Makeroni/Eye-of-Horus/version_2/hardware/3D_Model/Covers/Camera_Frontal-Bracket-Cover_1/Texture/Texture-Camera_Frontal-Bracket-Cover_1-v0_00.jpg

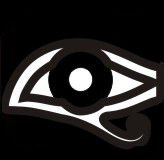
version_2/hardware/3D_Model/Covers/Camera_Frontal-Bracket-Cover_1/Texture/Texture-Camera_Frontal-Bracket-Cover_1-v0_00.jpg
