Makeroni/Eye-of-Horus/version_2/hardware/3D_Model/Covers/EoH_BackPack-Cover_1/Textures/EoH_BackPack-Cover_1-v0_00.jpg

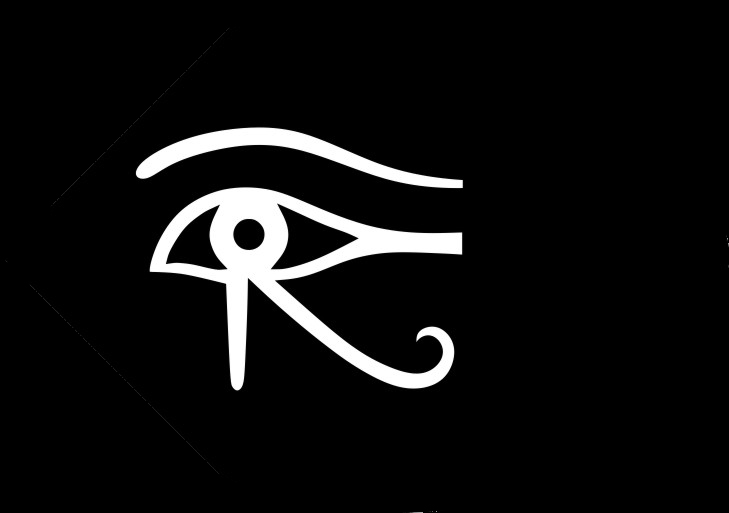
version_2/hardware/3D_Model/Covers/EoH_BackPack-Cover_1/Textures/EoH_BackPack-Cover_1-v0_00.jpg
