Makeroni/Eye-of-Horus/version_2/hardware/3D_Model/Materia_Prima/BREAKOUT_LIPO_CHARGER/Textures/Texture_Top.jpg

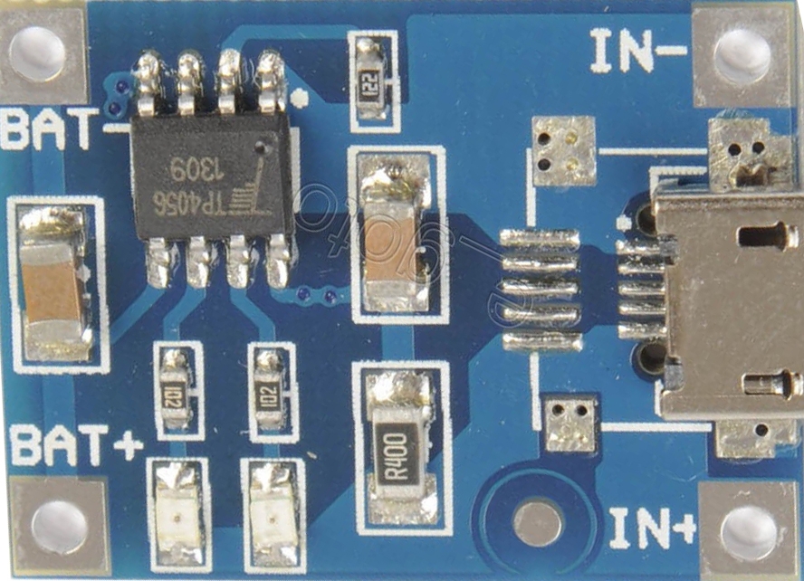
version_2/hardware/3D_Model/Materia_Prima/BREAKOUT_LIPO_CHARGER/Textures/Texture_Top.jpg
