Makeroni/Eye-of-Horus/version_2/hardware/3D_Model/Materia_Prima/DC_DC-Converter/Texture/DC_DC-Converter-Texture_Top.jpg

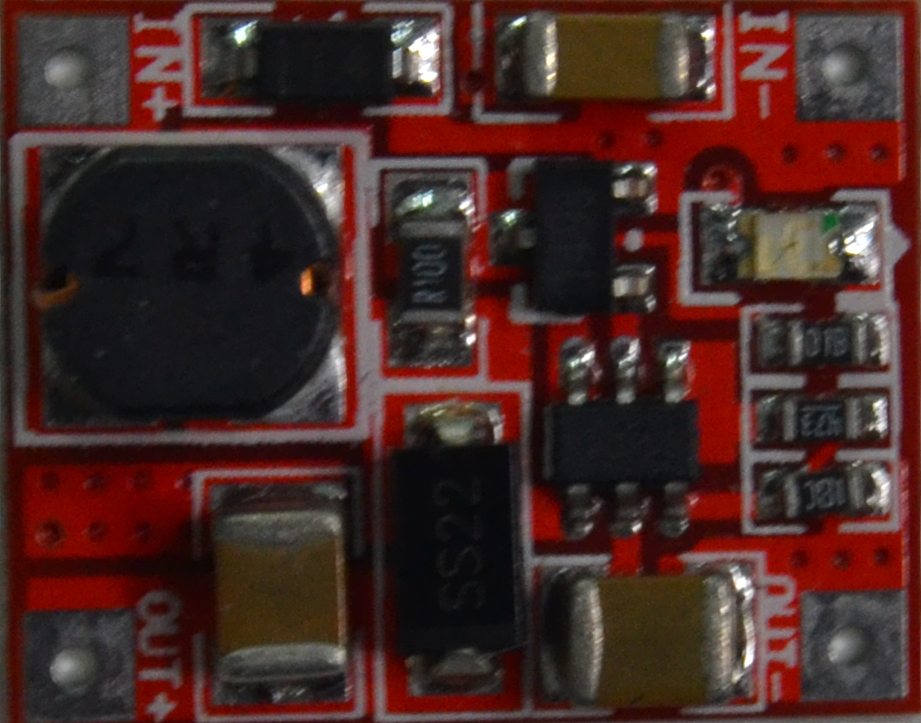
version_2/hardware/3D_Model/Materia_Prima/DC_DC-Converter/Texture/DC_DC-Converter-Texture_Top.jpg
