Makeroni/Eye-of-Horus/version_2/hardware/3D_Model/Materia_Prima/HUB_USB-2.0/Texture/HUB_USB-2_0-Texture_Bot.jpg

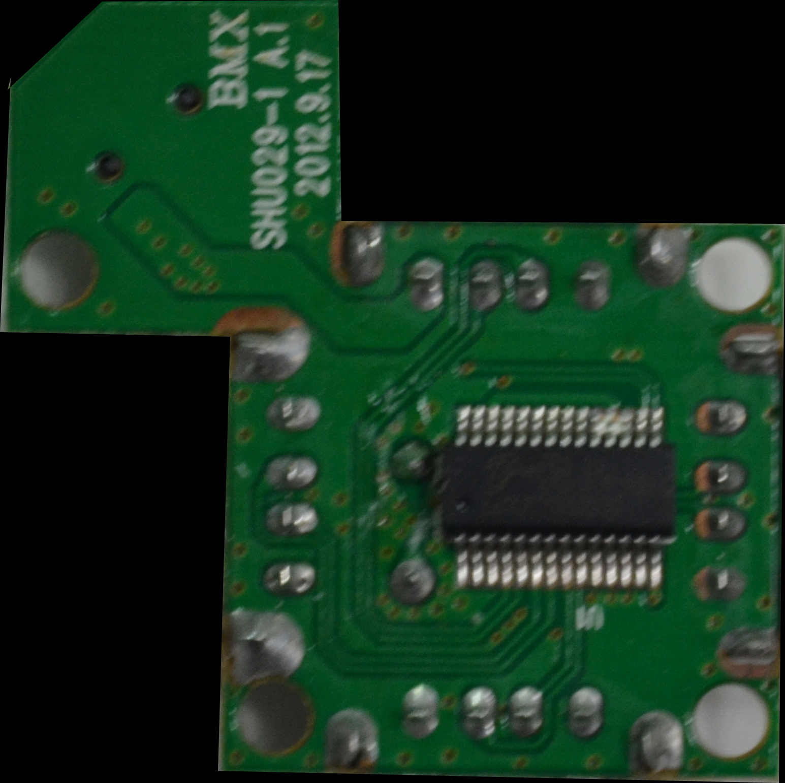
version_2/hardware/3D_Model/Materia_Prima/HUB_USB-2.0/Texture/HUB_USB-2_0-Texture_Bot.jpg
