Makeroni/Eye-of-Horus/version_2/hardware/3D_Model/Materia_Prima/Images/DSC_0015.JPG

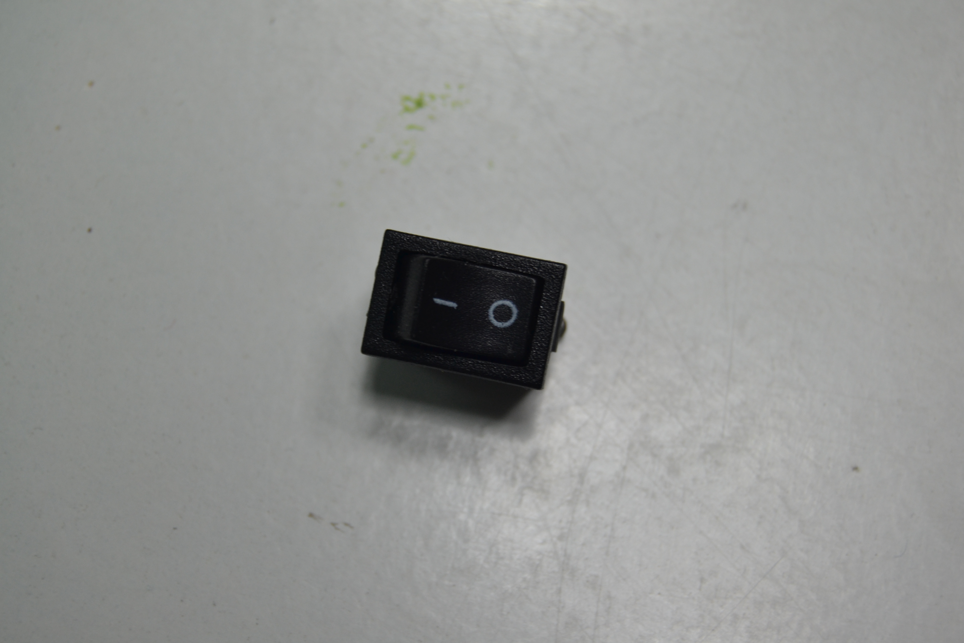
version_2/hardware/3D_Model/Materia_Prima/Images/DSC_0015.JPG
