Makeroni/Eye-of-Horus/version_2/hardware/3D_Model/Materia_Prima/SAMSUNG_BATTERY_AB563840CU-1000mAh-3_7V/Texture/SAMSUNG_BATTERY_AB563840CU-1000mAh-3_7V-Terture_Top.jpg

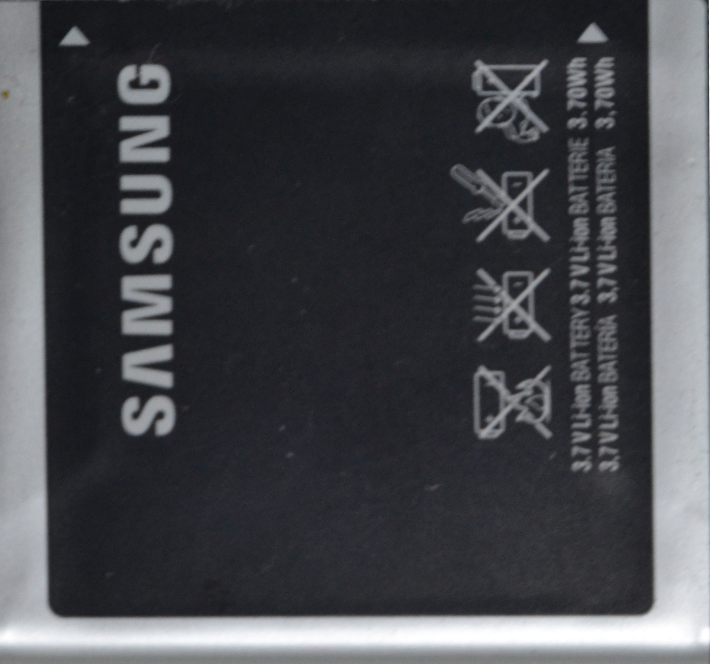
version_2/hardware/3D_Model/Materia_Prima/SAMSUNG_BATTERY_AB563840CU-1000mAh-3_7V/Texture/SAMSUNG_BATTERY_AB563840CU-1000mAh-3_7V-Terture_Top.jpg
