Makeroni/Eye-of-Horus/version_2/hardware/3D_Model/Materia_Prima/Textures/Images/DSC_0010.JPG

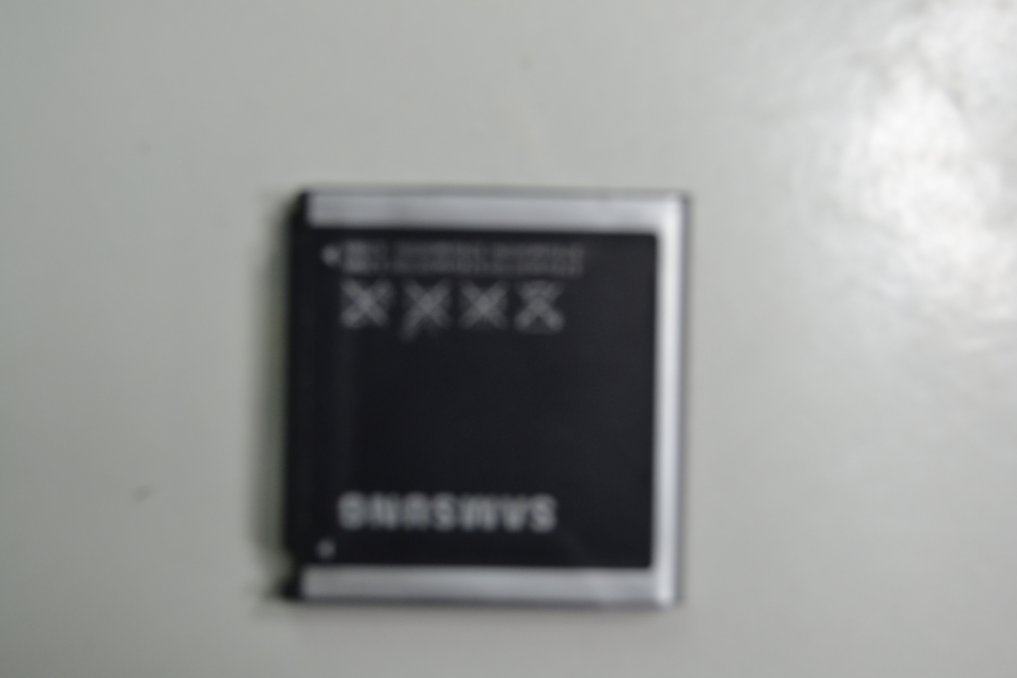
version_2/hardware/3D_Model/Materia_Prima/Textures/Images/DSC_0010.JPG
