Makeroni/Eye-of-Horus/version_2/hardware/3D_Model/Materia_Prima/Vocore_v1_0/Texture/Vocore_v1_0-Texture_Top.jpg

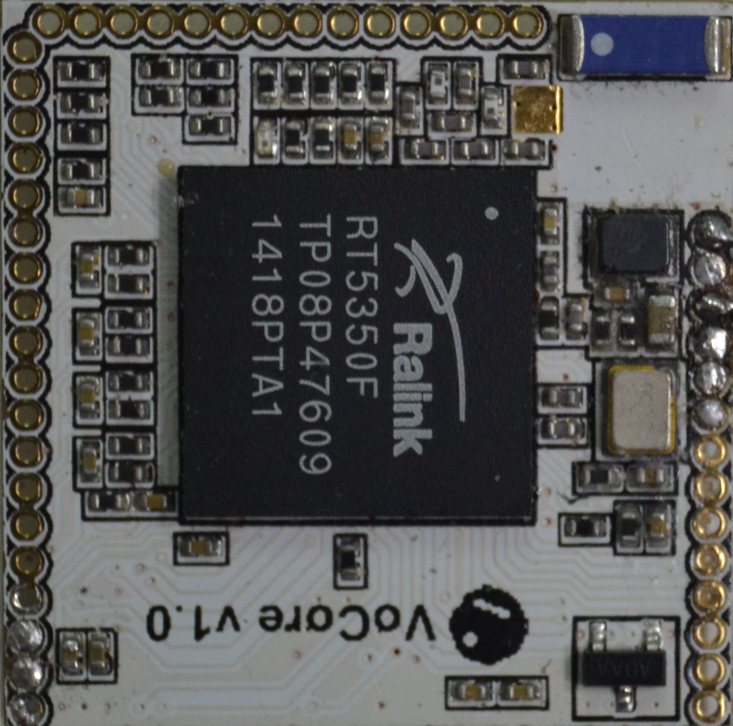
version_2/hardware/3D_Model/Materia_Prima/Vocore_v1_0/Texture/Vocore_v1_0-Texture_Top.jpg
