Makeroni/Eye-of-Horus/version_2/software/processing_apps/eoh_demo_1/data/4x4_384_15.gif

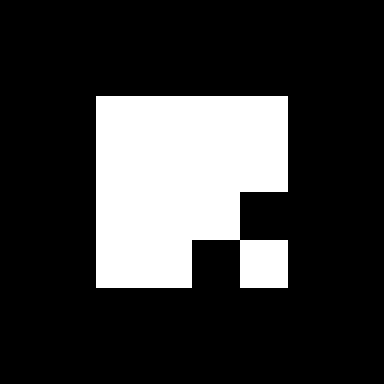
version_2/software/processing_apps/eoh_demo_1/data/4x4_384_15.gif
