Makeroni/Eye-of-Horus/version_2/software/processing_apps/eoh_demo_3/data/4x4_384_43.gif

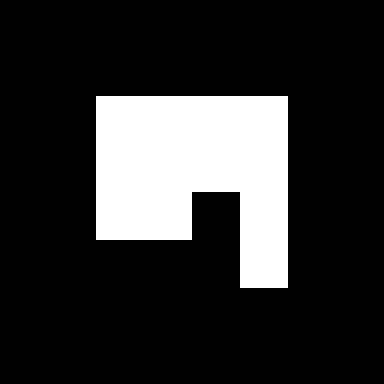
version_2/software/processing_apps/eoh_demo_3/data/4x4_384_43.gif
