Makeroni/Eye-of-Horus/version_2/software/processing_apps/eoh_demo_3/data/mario.png

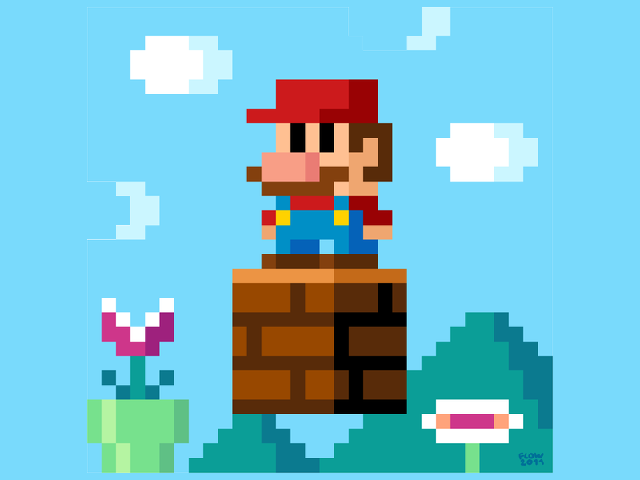
version_2/software/processing_apps/eoh_demo_3/data/mario.png
