Makeroni/Eye-of-Horus/version_2/software/processing_apps/materials/fiducials/examples/gif/4x4_384_67.gif

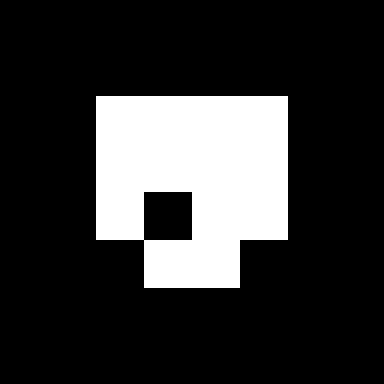
version_2/software/processing_apps/materials/fiducials/examples/gif/4x4_384_67.gif
