Makeroni/Eye-of-Horus/version_2/hardware/3D_Model/Output/STLs/Equipo_EoH-Montaje_v2_03-BLOCK-STL-M05P05.stl

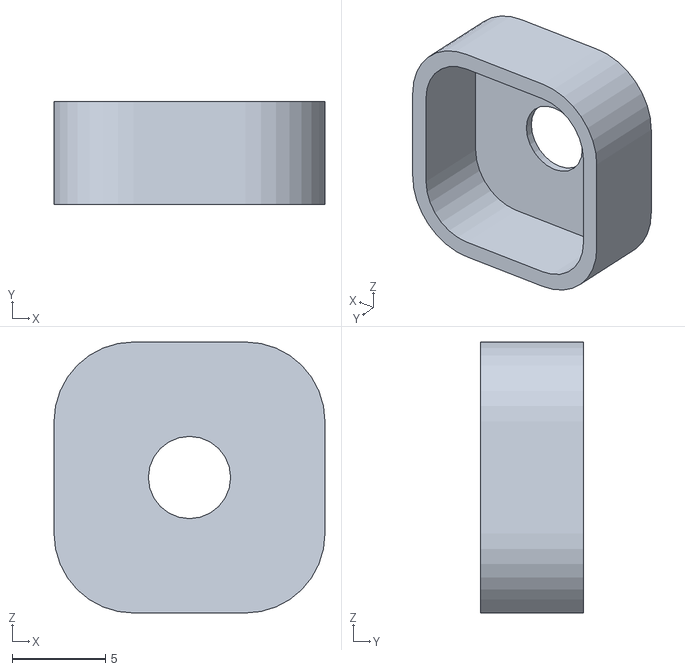
[picture p28: CAD file, 2015-09-20]
version_2/hardware/3D_Model/Output/STLs/Equipo_EoH-Montaje_v2_03-BLOCK-STL-M05P05.stl
14.5 x 5.50 x 14.5
