Makeroni/Eye-of-Horus/version_2/hardware/3D_Model/Output/STLs/Equipo_EoH-Montaje_v2_03-BLOCK-STL-M02P02.stl

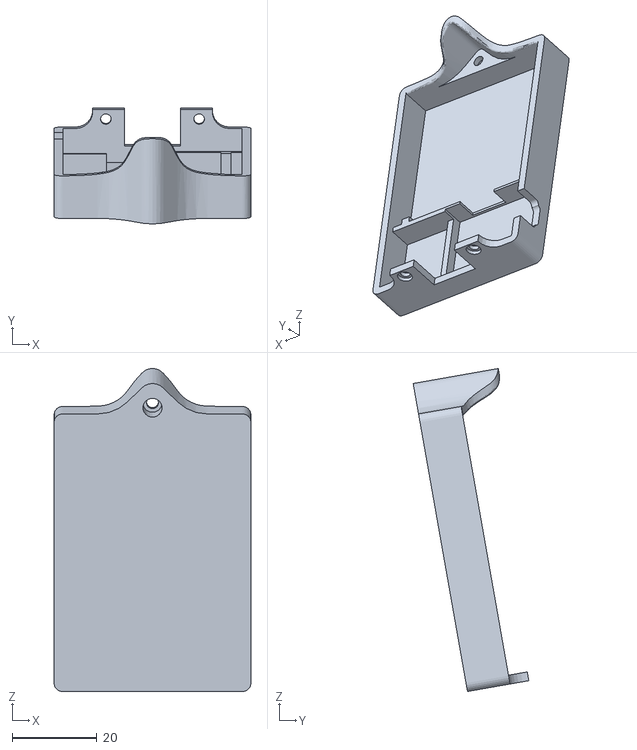
[picture p29: CAD file, 2015-09-20]
version_2/hardware/3D_Model/Output/STLs/Equipo_EoH-Montaje_v2_03-BLOCK-STL-M02P02.stl
46.5 x 27.3 x 76.2
