Makeroni/Eye-of-Horus/version_2/hardware/3D_Model/STLs/Camera_IR-Support_v1_16-Part_02.stl

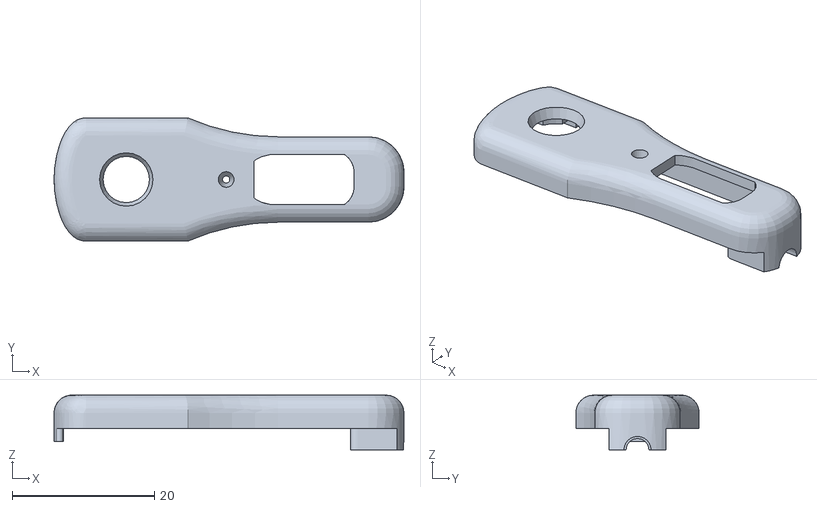
[picture p30: CAD file, 2015-09-20]
version_2/hardware/3D_Model/STLs/Camera_IR-Support_v1_16-Part_02.stl
49.1 x 17.3 x 7.70
