Makeroni/Eye-of-Horus/version_2/hardware/3D_Model/Output/STLs/Equipo_EoH-Montaje_v2_03-BLOCK-STL-M03P01.stl

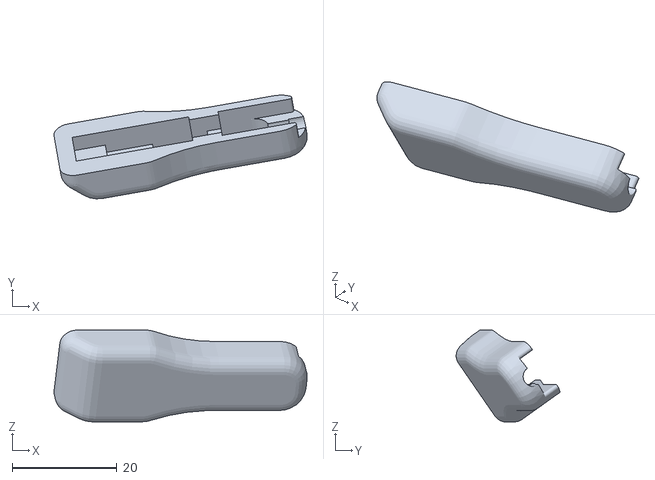
[picture p31: CAD file, 2015-09-20]
version_2/hardware/3D_Model/Output/STLs/Equipo_EoH-Montaje_v2_03-BLOCK-STL-M03P01.stl
48.3 x 19.8 x 17.5
