Makeroni/Eye-of-Horus/version_2/hardware/3D_Model/Output/STLs/Camera_IR-Support_v1_05-M03P2.stl

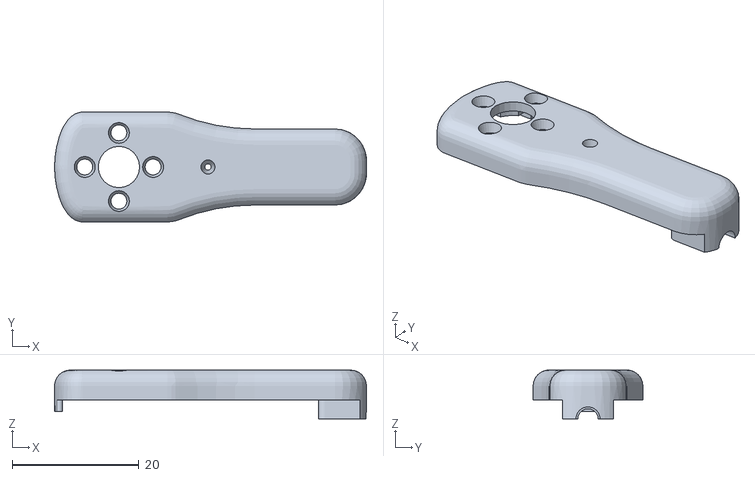
[picture p32: CAD file, 2015-09-20]
version_2/hardware/3D_Model/Output/STLs/Camera_IR-Support_v1_05-M03P2.stl
49.1 x 17.3 x 7.70
