Makeroni/Eye-of-Horus/version_2/hardware/3D_Model/STLs/EoH_BackPack_v2_015-Part_01.stl

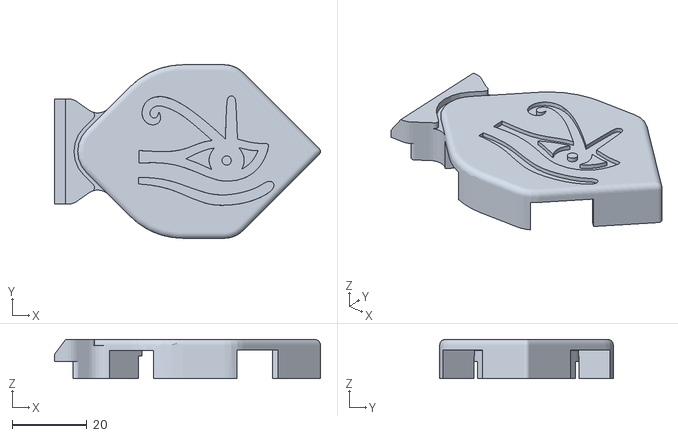
[picture p33: CAD file, 2015-09-20]
version_2/hardware/3D_Model/STLs/EoH_BackPack_v2_015-Part_01.stl
71.2 x 46.4 x 10.5
