Makeroni/Eye-of-Horus/version_2/hardware/3D_Model/Output/STLs/Equipo_EoH-Montaje_v2_03-BLOCK-STL-M05P01.stl

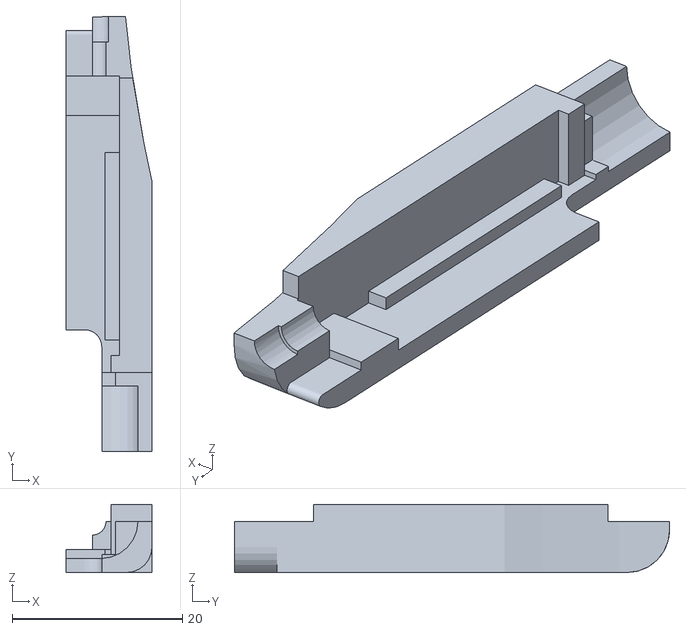
[picture p35: CAD file, 2015-09-20]
version_2/hardware/3D_Model/Output/STLs/Equipo_EoH-Montaje_v2_03-BLOCK-STL-M05P01.stl
10.1 x 51.1 x 8.00
