Makeroni/Eye-of-Horus/version_2/hardware/3D_Model/STLs/EoH_BackPack_v2_015-Part_03.stl

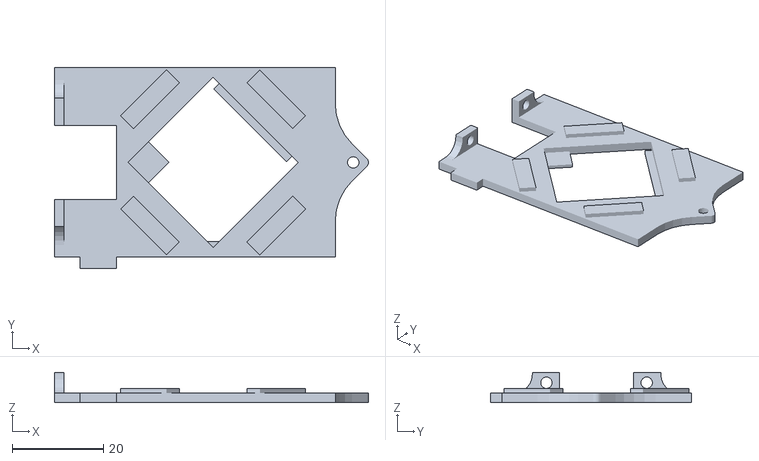
[picture p36: CAD file, 2015-09-20]
version_2/hardware/3D_Model/STLs/EoH_BackPack_v2_015-Part_03.stl
68.9 x 44.0 x 6.60
