Makeroni/Eye-of-Horus/version_2/hardware/3D_Model/Output/STLs/Equipo_EoH-Montaje_v2_03-BLOCK-STL-M01P03.stl

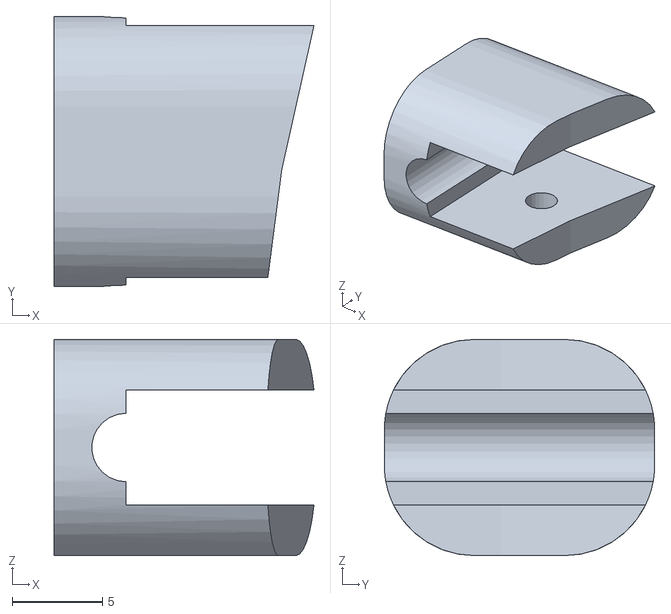
[picture p37: CAD file, 2015-09-20]
version_2/hardware/3D_Model/Output/STLs/Equipo_EoH-Montaje_v2_03-BLOCK-STL-M01P03.stl
14.4 x 15.0 x 12.0
