Makeroni/Eye-of-Horus/version_2/hardware/3D_Model/STLs/EoH_BackPack_v2_013-OUTPUT-Part_02.stl

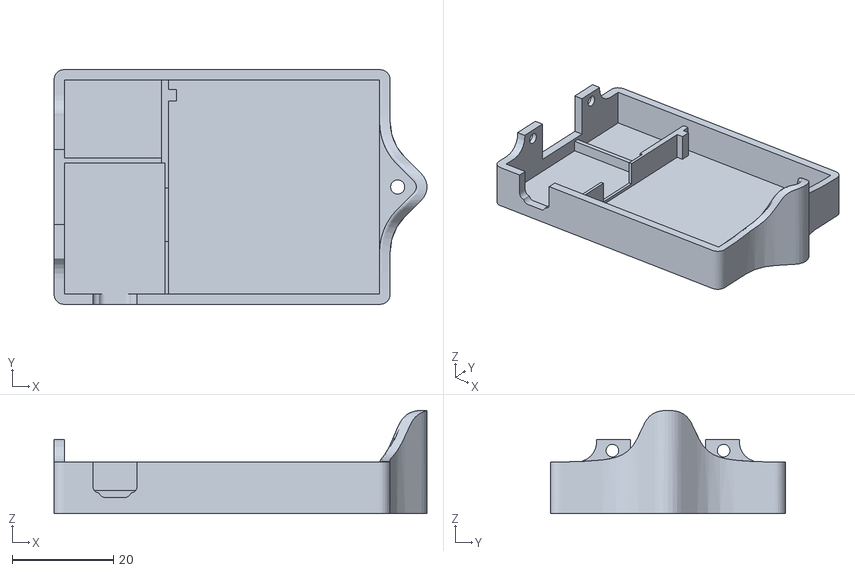
[picture p38: CAD file, 2015-09-20]
version_2/hardware/3D_Model/STLs/EoH_BackPack_v2_013-OUTPUT-Part_02.stl
73.8 x 46.4 x 20.4
