Makeroni/Eye-of-Horus/version_2/hardware/3D_Model/STLs/Camera_IR-Support_v1_16-Part_01.stl

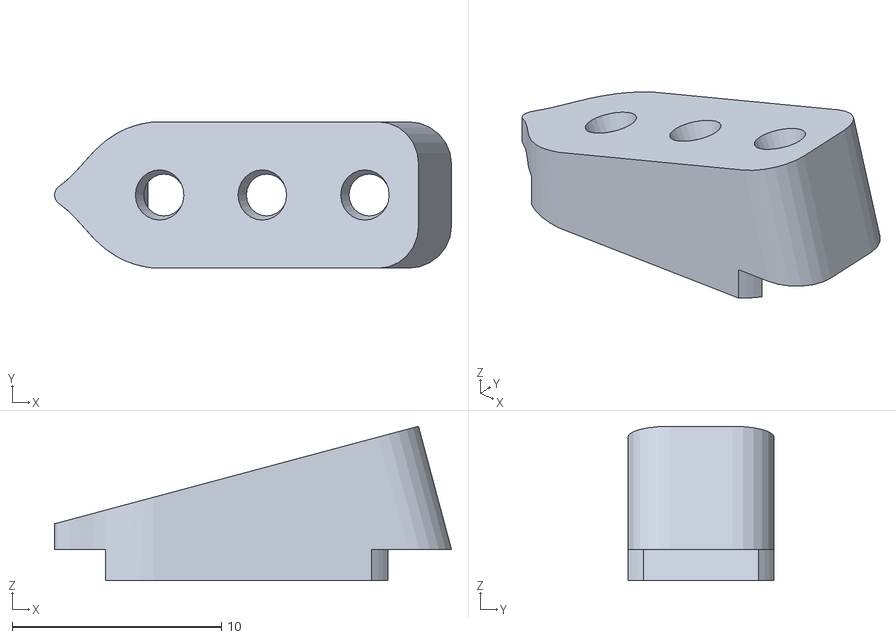
[picture p39: CAD file, 2015-09-20]
version_2/hardware/3D_Model/STLs/Camera_IR-Support_v1_16-Part_01.stl
19.0 x 7.00 x 7.38
