Makeroni/Eye-of-Horus/version_2/hardware/3D_Model/STLs/Camera_IR-Support_v1_16-Part_03.stl

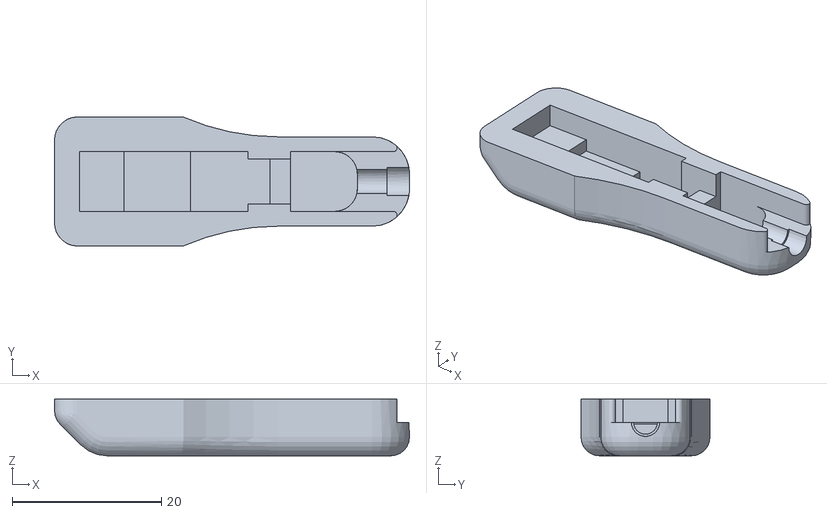
[picture p41: CAD file, 2015-09-20]
version_2/hardware/3D_Model/STLs/Camera_IR-Support_v1_16-Part_03.stl
47.7 x 17.3 x 7.60
