Makeroni/Eye-of-Horus/version_2/hardware/3D_Model/Equipo_EoH/Equipo_EoH-Montaje-Bloque_v1_00.stl

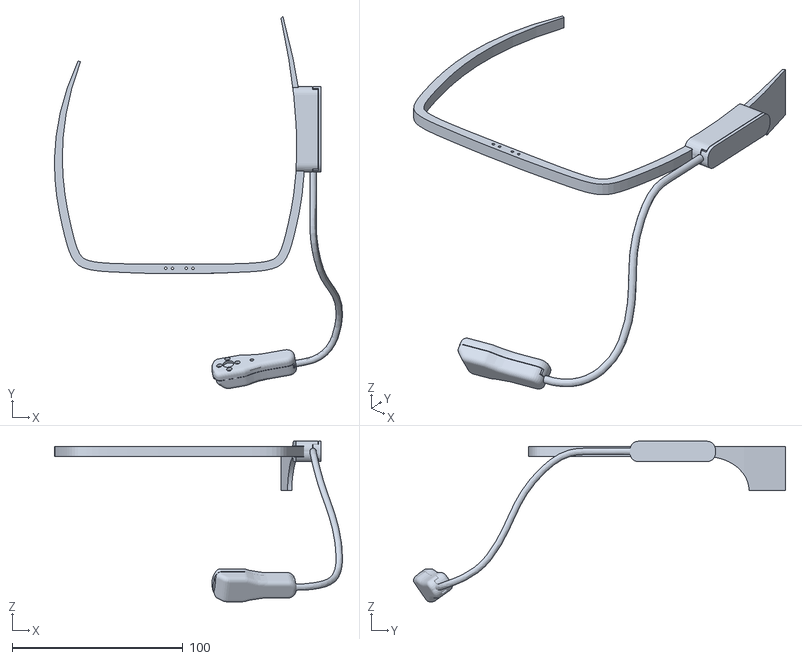
[picture p43: CAD file, 2015-04-19]
version_2/hardware/3D_Model/Equipo_EoH/Equipo_EoH-Montaje-Bloque_v1_00.stl
168.7 x 217.9 x 94.1
