Makeroni/Eye-of-Horus/version_2/hardware/3D_Model/STLs/Camera_IR-Bracket-Part_02.stl

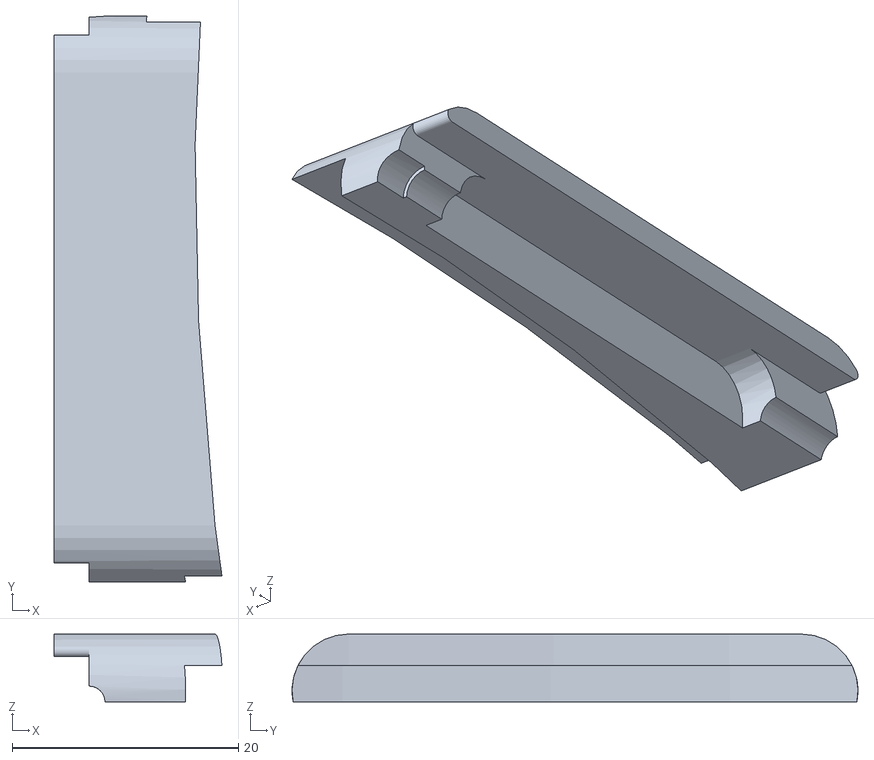
[picture p44: CAD file, 2015-04-19]
version_2/hardware/3D_Model/STLs/Camera_IR-Bracket-Part_02.stl
14.8 x 50.0 x 6.00
