Makeroni/Eye-of-Horus/version_2/hardware/3D_Model/STLs/Camera_IR-Glasses_v1_00.stl

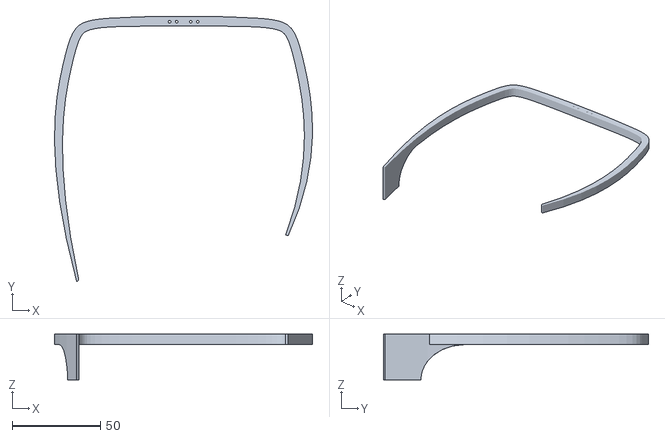
[picture p46: CAD file, 2015-04-19]
version_2/hardware/3D_Model/STLs/Camera_IR-Glasses_v1_00.stl
146.4 x 150.6 x 26.0
