Makeroni/Eye-of-Horus/version_2/hardware/3D_Model/STLs/Camera_IR-Bracket-Part_01.stl

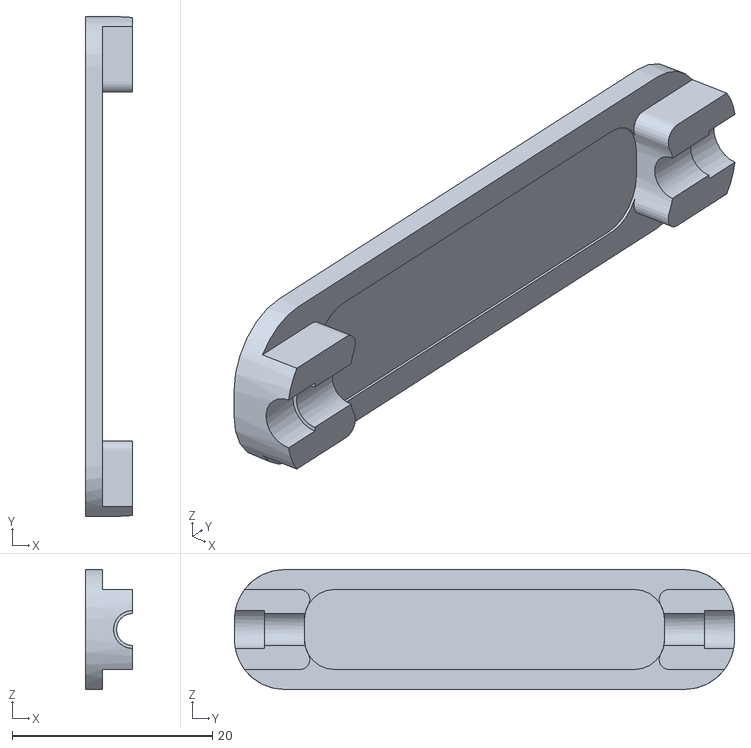
[picture p48: CAD file, 2015-04-19]
version_2/hardware/3D_Model/STLs/Camera_IR-Bracket-Part_01.stl
4.70 x 50.0 x 12.0
