Makeroni/Eye-of-Horus/version_2/hardware/3D_Model/Output/Output-Equipo_EoH-Montaje_v2_16-Transfer/Camera_IR-Support_v1_16-Render_01.pdf

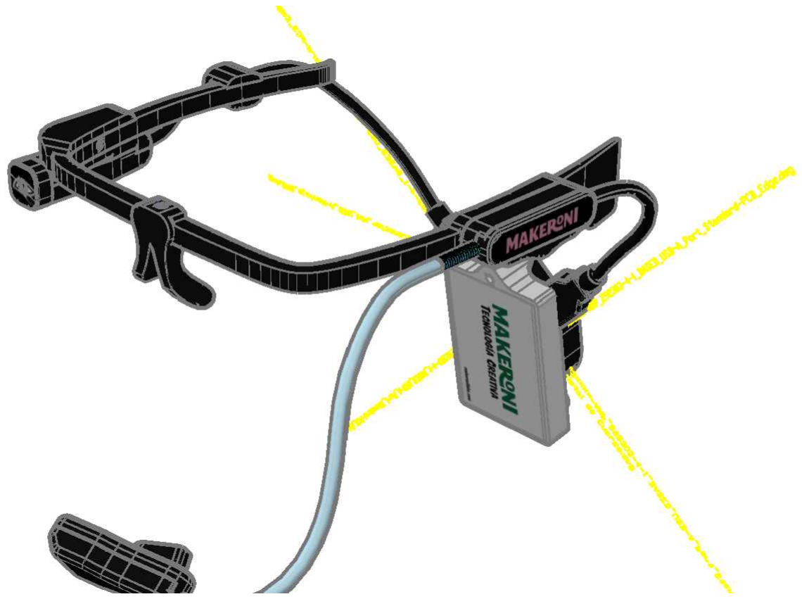
[picture p56: figure]
