Makeroni/Eye-of-Horus/version_2/hardware/3D_Model/Output/Output_pdf/Equipo_EoH-Montaje_v1_01-Render_00.pdf

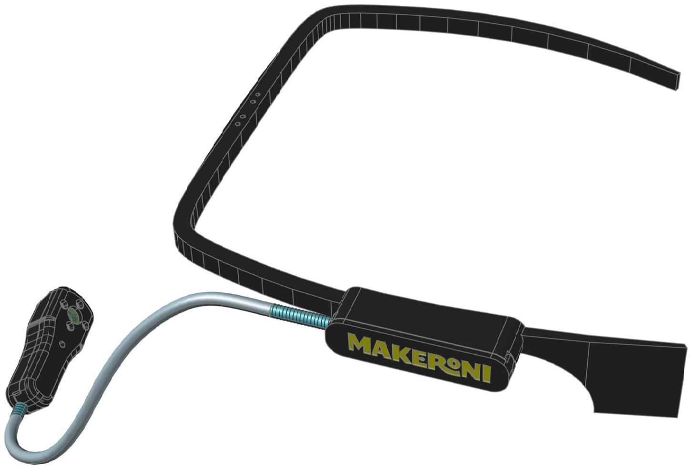
[picture p57: page 1]
