Makeroni/Eye-of-Horus/version_2/hardware/3D_Model/Output/Output_pdf/Equipo_EoH-Montaje_v1_01-Render_01.pdf

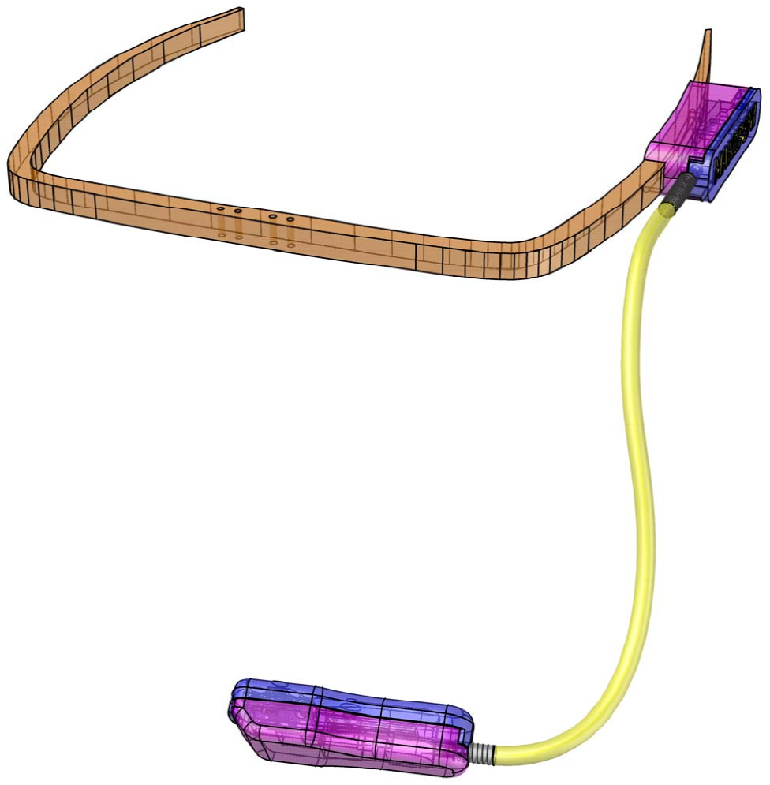
[picture p58: page 1]
