Makeroni/Eye-of-Horus/version_2/hardware/3D_Model/Output/Output_pdf/Equipo_EoH-Montaje_v1_01-Render_03.pdf

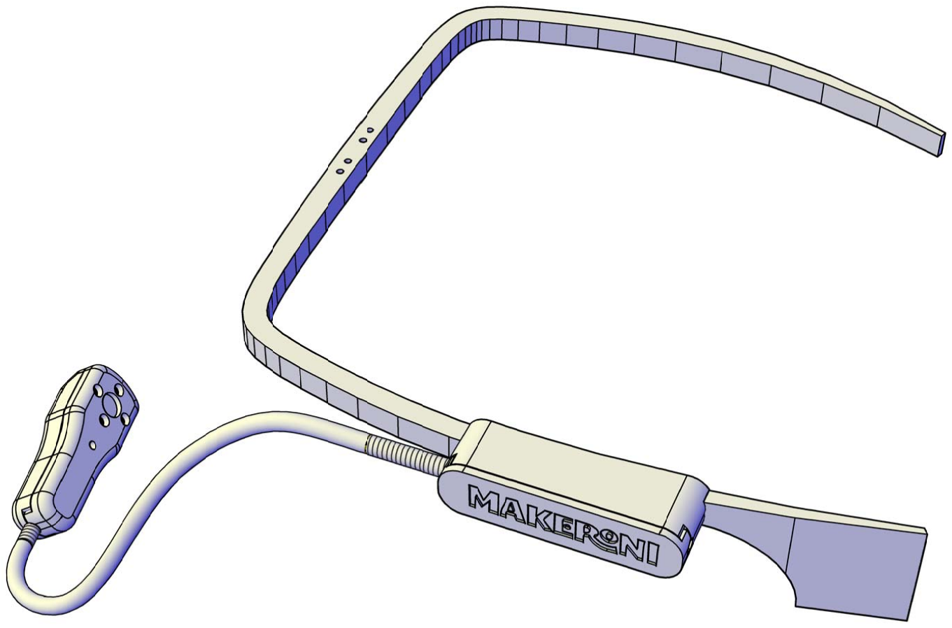
[picture p59: page 1]
