Makeroni/Eye-of-Horus/version_2/hardware/3D_Model/Output/Output_jpg/Equipo_EoH-Montaje_v1_01-Render_01.jpg

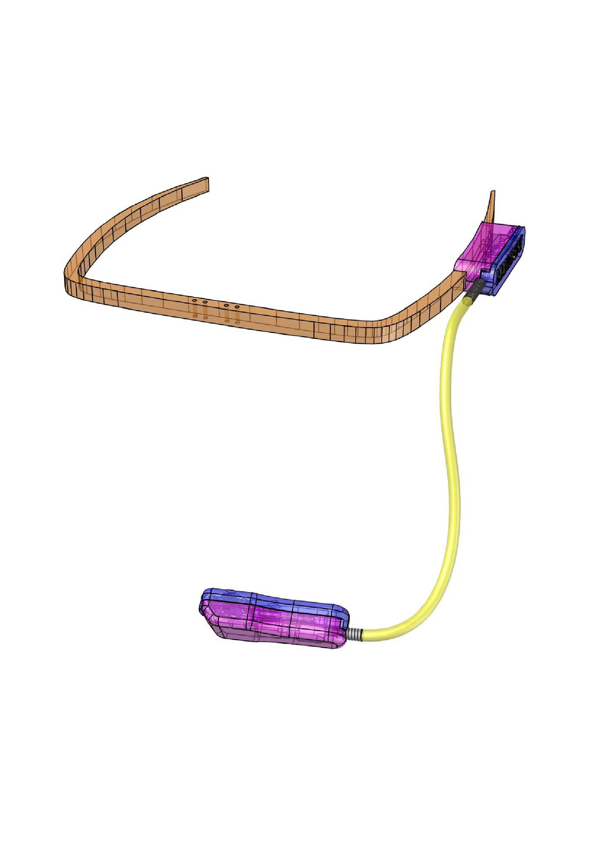
version_2/hardware/3D_Model/Output/Output_jpg/Equipo_EoH-Montaje_v1_01-Render_01.jpg
