Makeroni/Eye-of-Horus/version_2/hardware/3D_Model/Output/Output-Equipo_EoH-Montaje_v2_16-Transfer/Camera_IR-Bracket_v1_04-Render_02.pdf

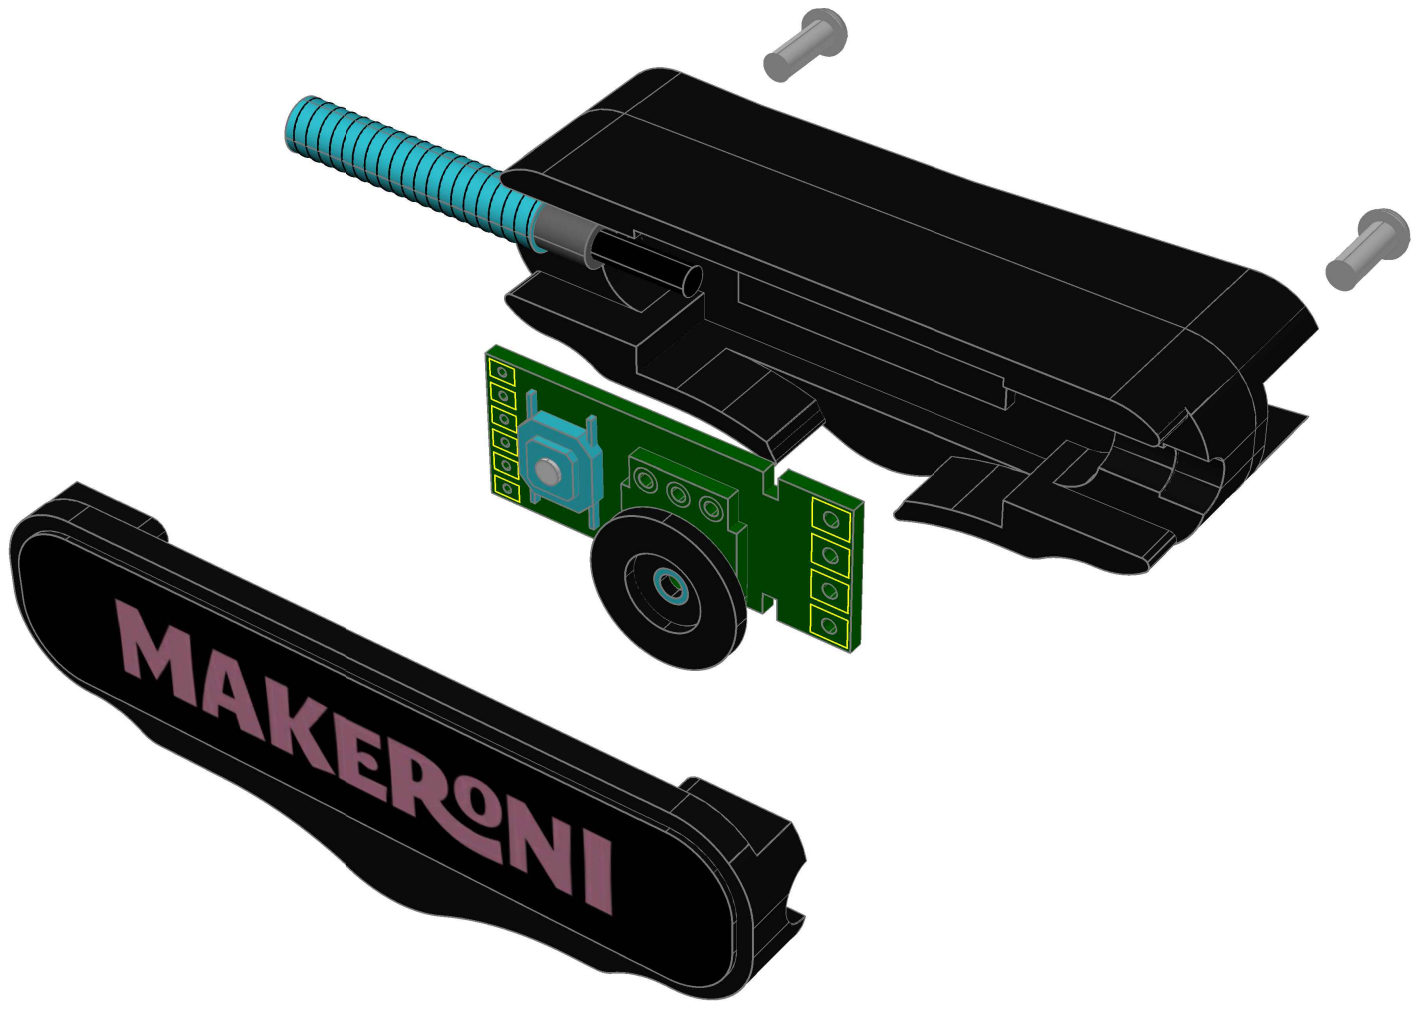
[picture p81: page 1]
