Makeroni/Eye-of-Horus/version_2/hardware/3D_Model/Output/Output-Equipo_EoH-Montaje_v2_16-Transfer/Camera_IR-Support_v1_16-Render_00.pdf

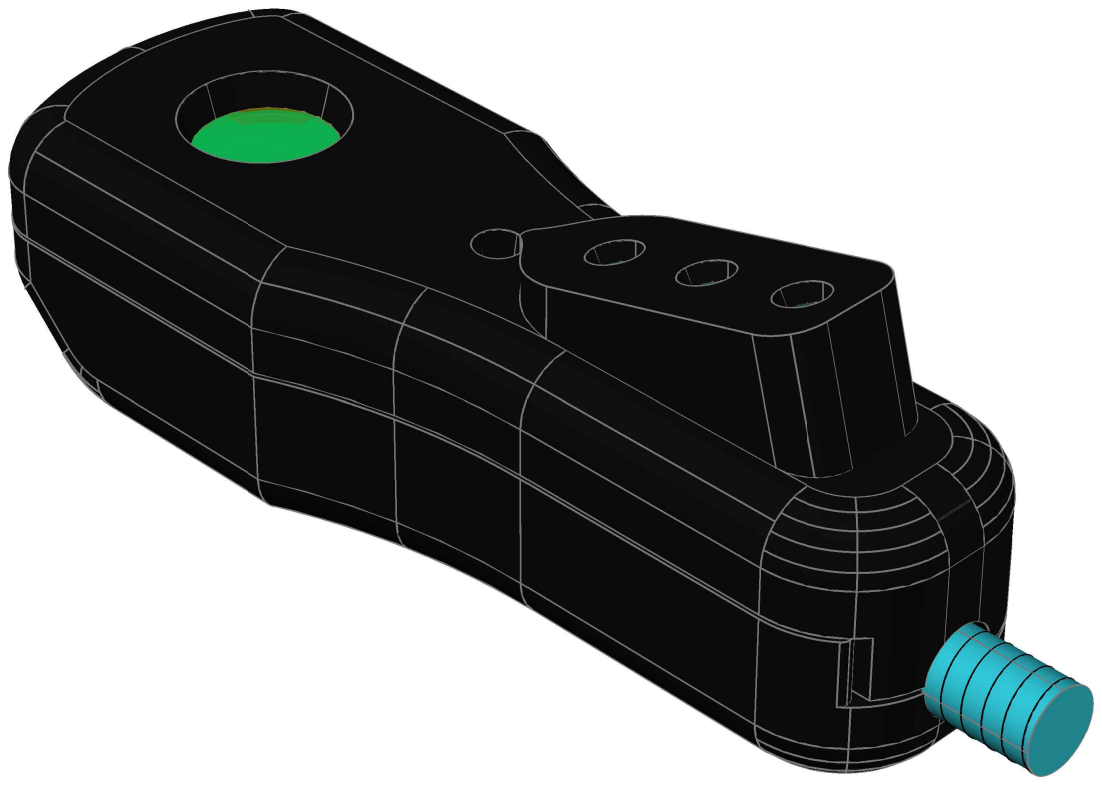
[picture p83: page 1]
