Makeroni/Eye-of-Horus/version_2/hardware/3D_Model/Output/Output-Equipo_EoH-Montaje_v2_16-Transfer/EoH_BackPack_v2_017-Render_03.pdf

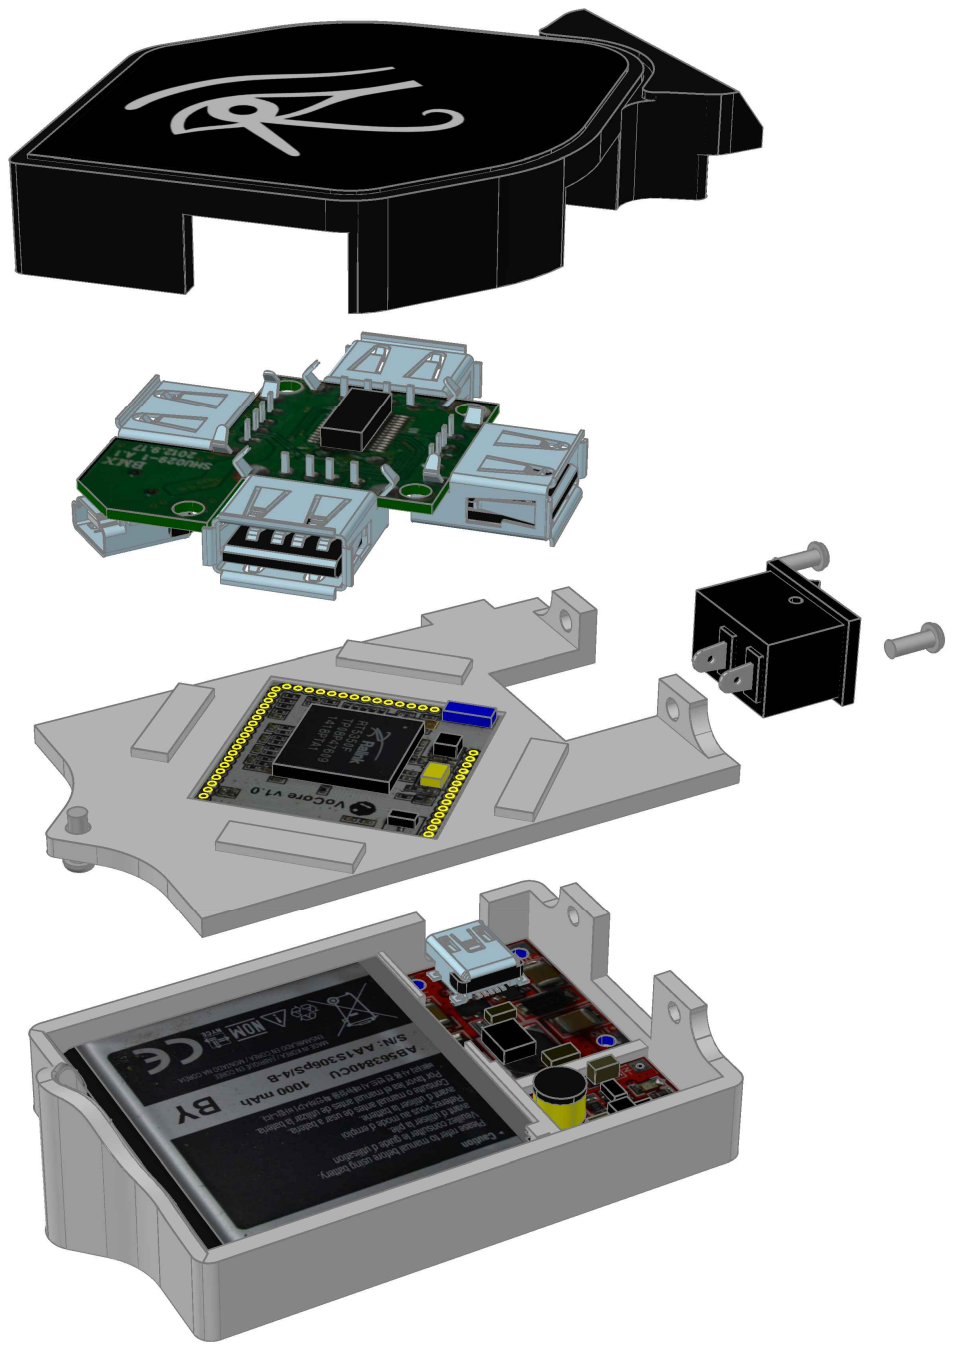
[picture p89: page 1]
