Makeroni/Eye-of-Horus/version_2/hardware/3D_Model/Output/Output-Equipo_EoH-Montaje_v2_16-Transfer/Equipo_EoH-Montaje_v2_16-Despiece_03.pdf

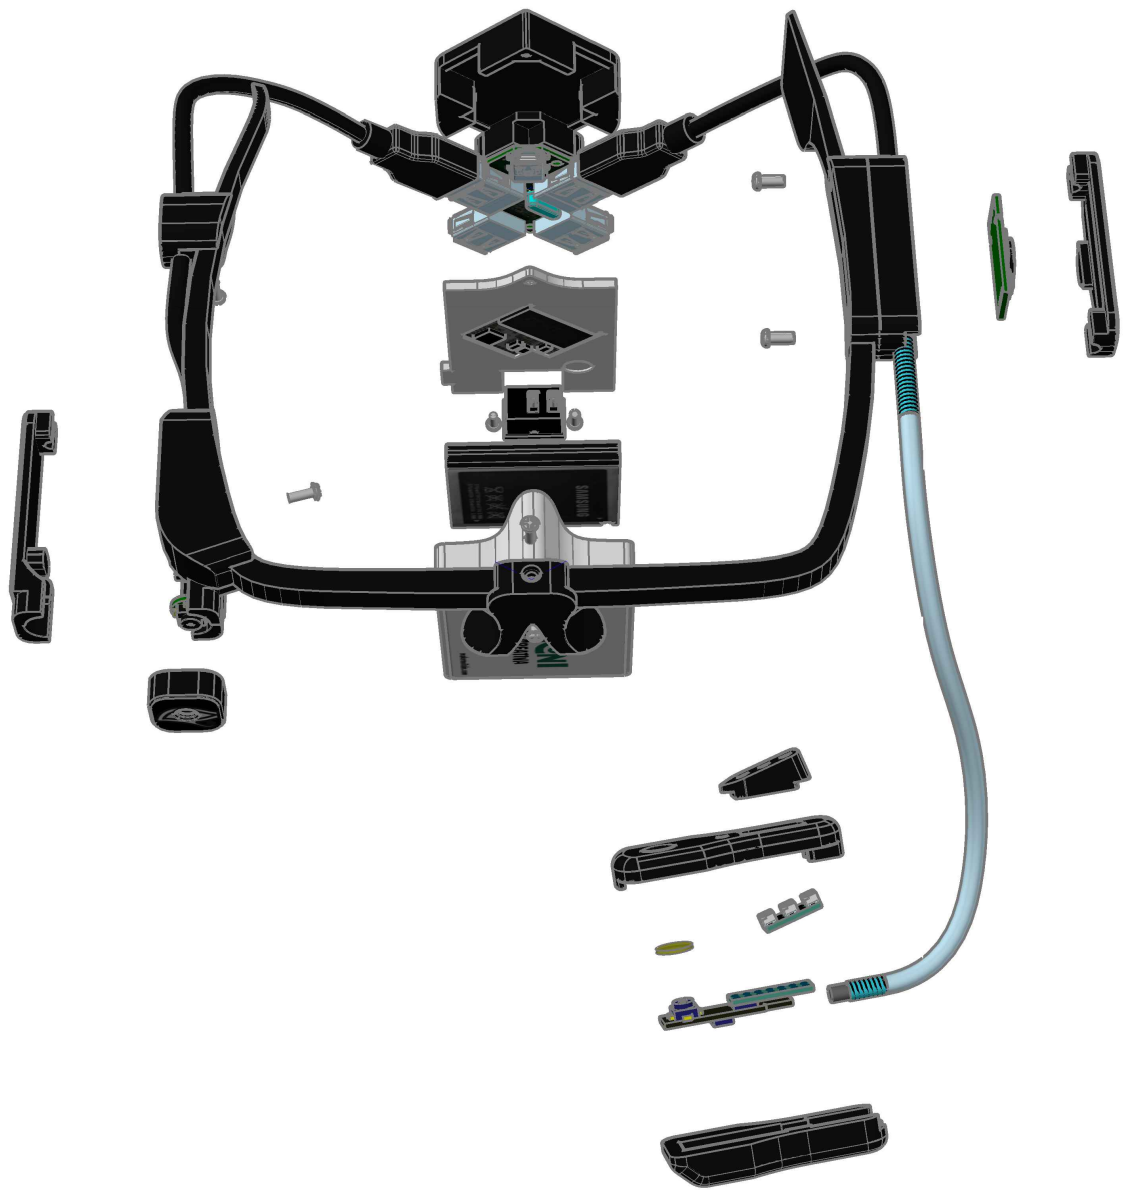
[picture p94: page 1]
