Makeroni/Eye-of-Horus/version_2/hardware/3D_Model/Output/Output-Equipo_EoH-Montaje_v2_16-Transfer/Equipo_EoH-Montaje_v2_16-Despiece_04.pdf

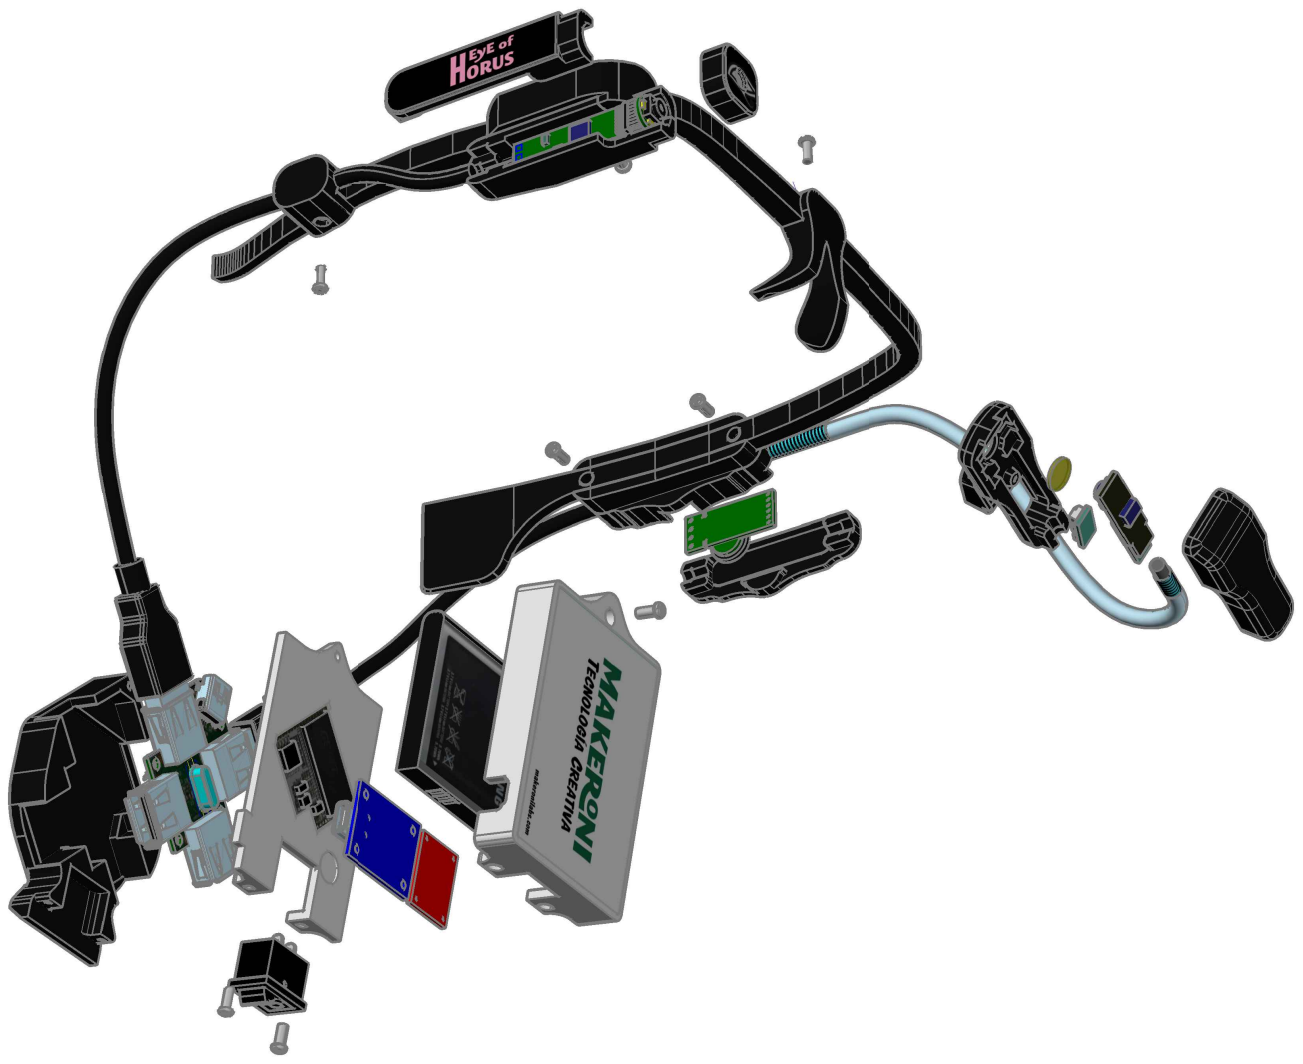
[picture p95: page 1]
