Makeroni/Eye-of-Horus/version_1/hardware/pcb_designs/eye_of_horus_v1_sch.pdf

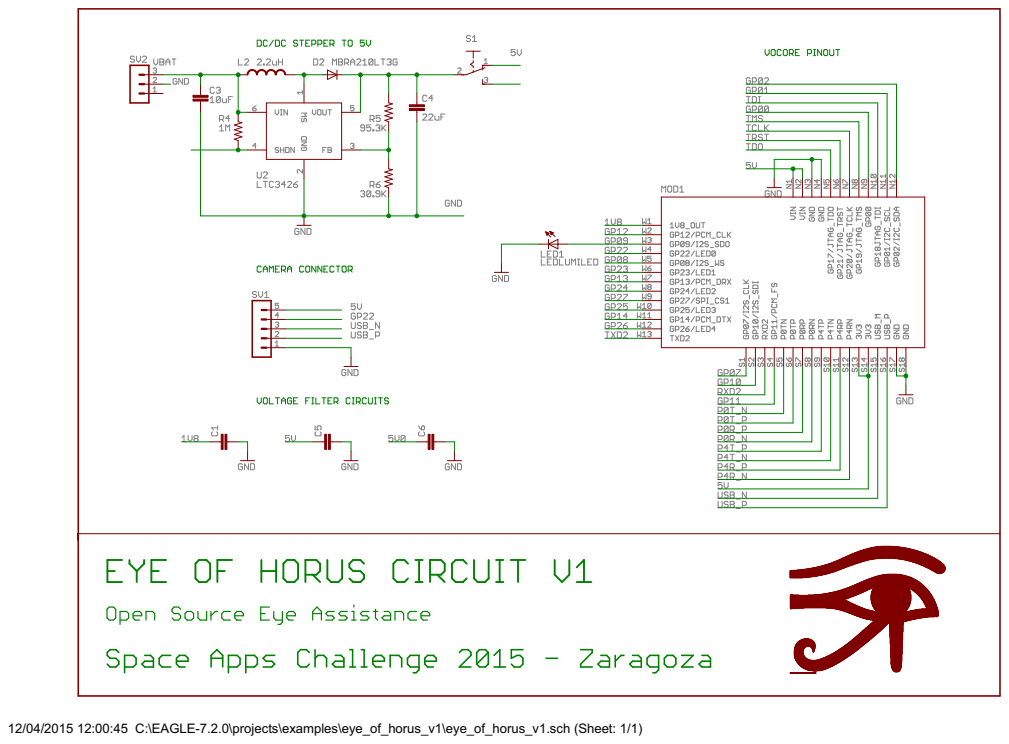
[picture p126: page 1]

12/04/2015 12:00:45 C:\EAGLE-7.2.0\projects\examples\eye_of_horus_v1\eye_of_horus_v1.sch (Sheet: 1/1)
