Makeroni/Eye-of-Horus/version_1/hardware/pcb_designs/vocore-v1.0.pdf

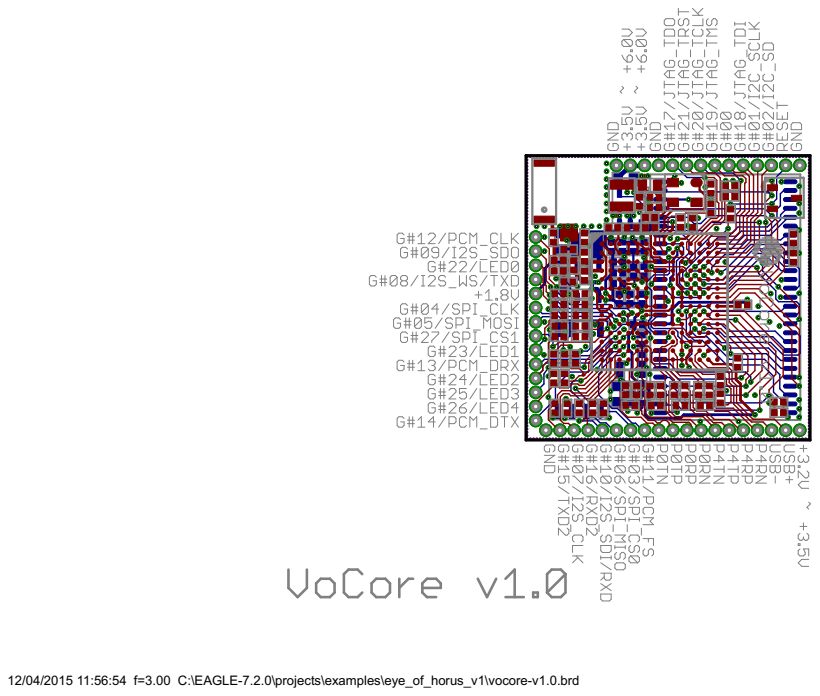
[picture p127: page 1]

12/04/2015 11:56:54 f=3.00 C:\EAGLE-7.2.0\projects\examples\eye_of_horus_v1\vocore-v1.0.brd
